JoaogSacerdote/CyberGame/assets/sprites/IMAGENS_ANTIGAS/empresa/AREA_DE_INTERACAO_BAIXO_DO_NPC_TI_NULL.png

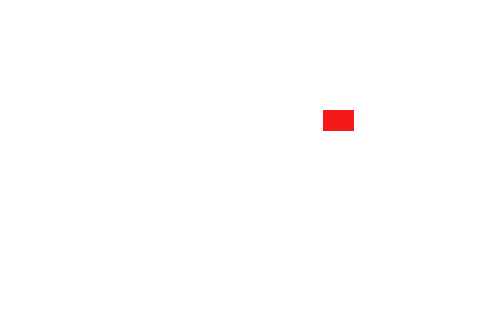
assets/sprites/IMAGENS_ANTIGAS/empresa/AREA_DE_INTERACAO_BAIXO_DO_NPC_TI_NULL.png
