JoaogSacerdote/CyberGame/assets/sprites/IMAGENS_ANTIGAS/empresa/AREA_DE_INTERACAO_PARA_TAREFA_VERDE_NULL.png

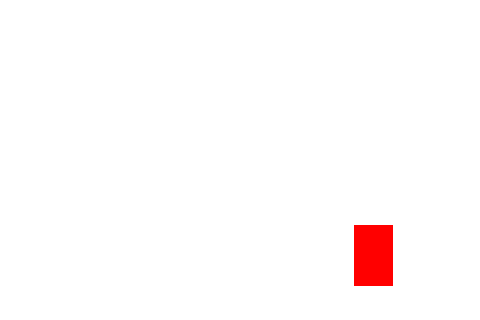
assets/sprites/IMAGENS_ANTIGAS/empresa/AREA_DE_INTERACAO_PARA_TAREFA_VERDE_NULL.png
