JoaogSacerdote/CyberGame/assets/sprites/IMAGENS_ANTIGAS/empresa/AREA_PORTA_RECEPCAO_NULL.png

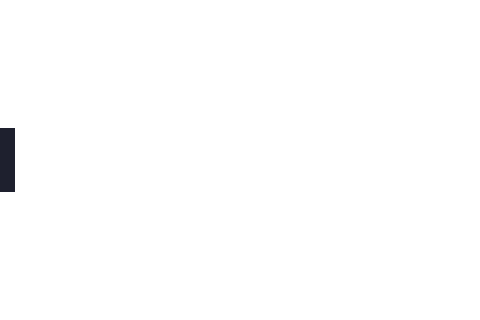
assets/sprites/IMAGENS_ANTIGAS/empresa/AREA_PORTA_RECEPCAO_NULL.png
