JoaogSacerdote/CyberGame/assets/sprites/IMAGENS_ANTIGAS/empresa/CHAO_02.png

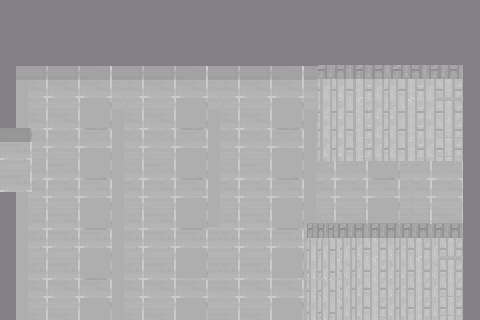
assets/sprites/IMAGENS_ANTIGAS/empresa/CHAO_02.png
