JoaogSacerdote/CyberGame/assets/sprites/IMAGENS_ANTIGAS/empresa/PAREDES.png

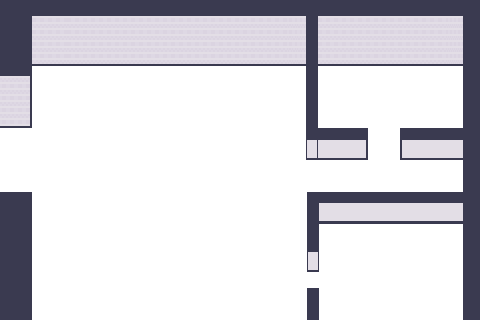
assets/sprites/IMAGENS_ANTIGAS/empresa/PAREDES.png
