JoaogSacerdote/CyberGame/assets/sprites/IMAGENS_ANTIGAS/empresa/PAREDES_E_OBJETOS_02.png

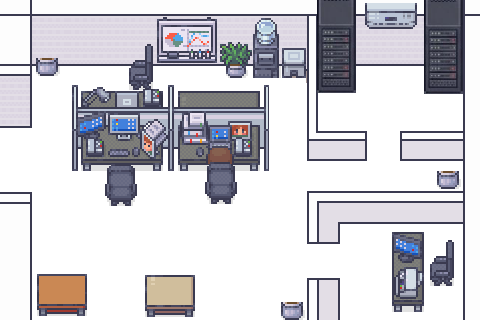
assets/sprites/IMAGENS_ANTIGAS/empresa/PAREDES_E_OBJETOS_02.png
