JoaogSacerdote/CyberGame/assets/sprites/IMAGENS_ANTIGAS/empresa/SPAWN_NULL.png

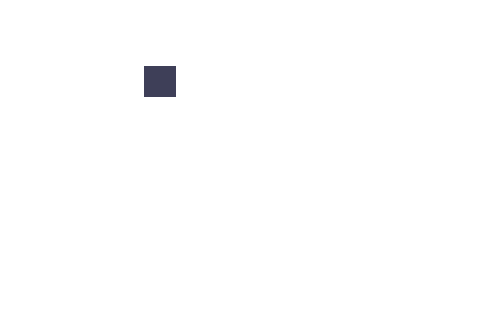
assets/sprites/IMAGENS_ANTIGAS/empresa/SPAWN_NULL.png
