JoaogSacerdote/CyberGame/assets/sprites/IMAGENS_ANTIGAS/recepcao/AREA_QUE_LIBERA_INTERACAO_COM_RECEPCIONISTA_NULL.png

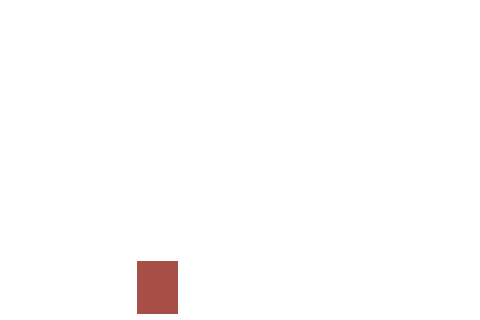
assets/sprites/IMAGENS_ANTIGAS/recepcao/AREA_QUE_LIBERA_INTERACAO_COM_RECEPCIONISTA_NULL.png
