JoaogSacerdote/CyberGame/assets/sprites/IMAGENS_ANTIGAS/recepcao/COMPLEMENTO_SEMCOLISAO_PAREDES_E_OBJETOS_03.png

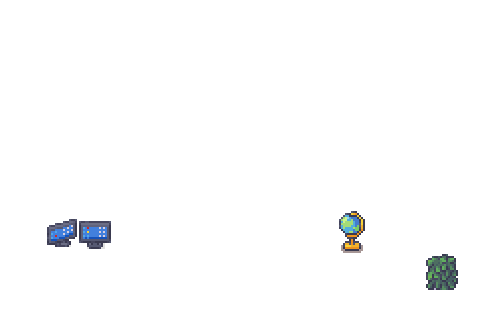
assets/sprites/IMAGENS_ANTIGAS/recepcao/COMPLEMENTO_SEMCOLISAO_PAREDES_E_OBJETOS_03.png
