JoaogSacerdote/CyberGame/assets/sprites/IMAGENS_ANTIGAS/recepcao/PAREDES.png

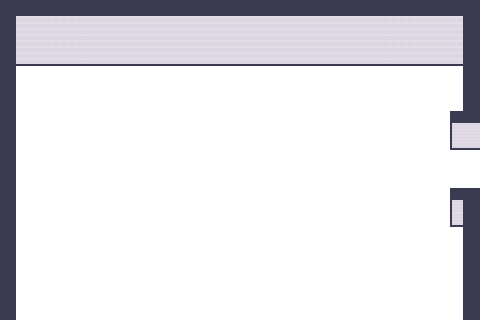
assets/sprites/IMAGENS_ANTIGAS/recepcao/PAREDES.png
