JoaogSacerdote/CyberGame/assets/sprites/IMAGENS_ANTIGAS/recepcao/PISO_CAMADA_00.png

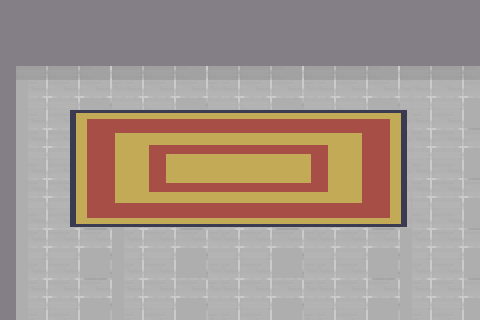
assets/sprites/IMAGENS_ANTIGAS/recepcao/PISO_CAMADA_00.png
