JoaogSacerdote/CyberGame/assets/sprites/IMAGENS_ANTIGAS/recepcao/RECEPCIONISTA_MECHENDO_NO_COMPUTADOR_SEM_INTERACAO_05.png

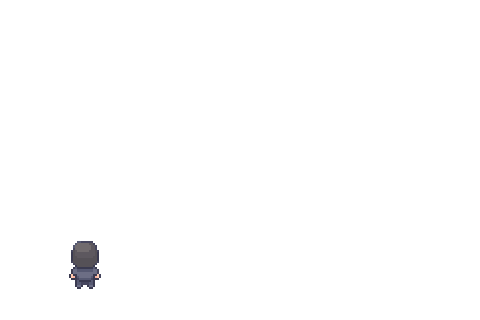
assets/sprites/IMAGENS_ANTIGAS/recepcao/RECEPCIONISTA_MECHENDO_NO_COMPUTADOR_SEM_INTERACAO_05.png
