JoaogSacerdote/CyberGame/assets/sprites/tarefas/CHIADO.png

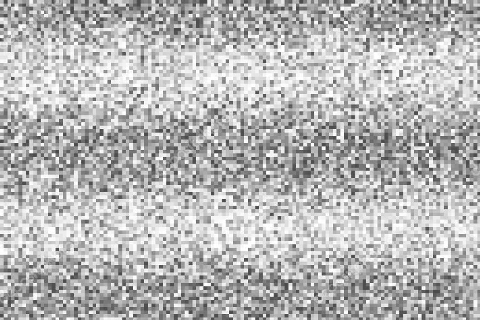
assets/sprites/tarefas/CHIADO.png
