JoaogSacerdote/CyberGame/assets/sprites/tarefas/CREDENCIAL_GERAL.png

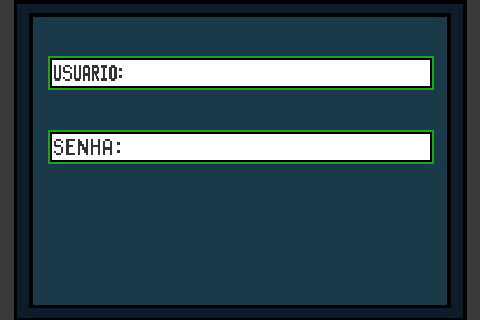
assets/sprites/tarefas/CREDENCIAL_GERAL.png
