JoaogSacerdote/CyberGame/assets/sprites/tarefas/FUNDO_TELA.png

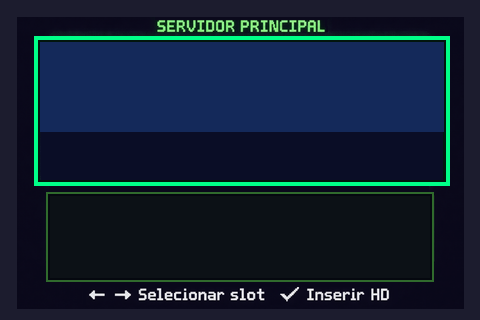
assets/sprites/tarefas/FUNDO_TELA.png
