JoaogSacerdote/CyberGame/assets/sprites/tarefas/SERVIDOR_FUNDO.png

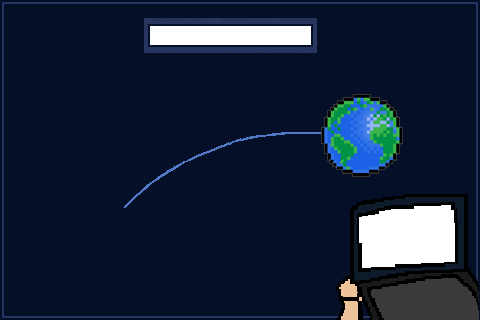
assets/sprites/tarefas/SERVIDOR_FUNDO.png
