JoaogSacerdote/CyberGame/assets/sprites/tarefas/TELA_DERROTA.png

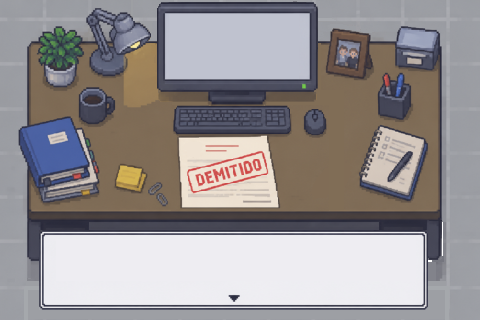
assets/sprites/tarefas/TELA_DERROTA.png
