JoaogSacerdote/CyberGame/assets/sprites/tarefas/TELA_VITORIA.png

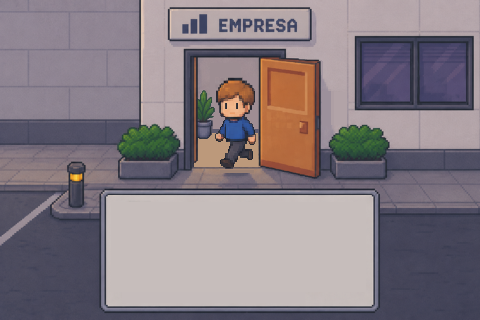
assets/sprites/tarefas/TELA_VITORIA.png
