JoaogSacerdote/CyberGame/simulation/img/Tela01.png

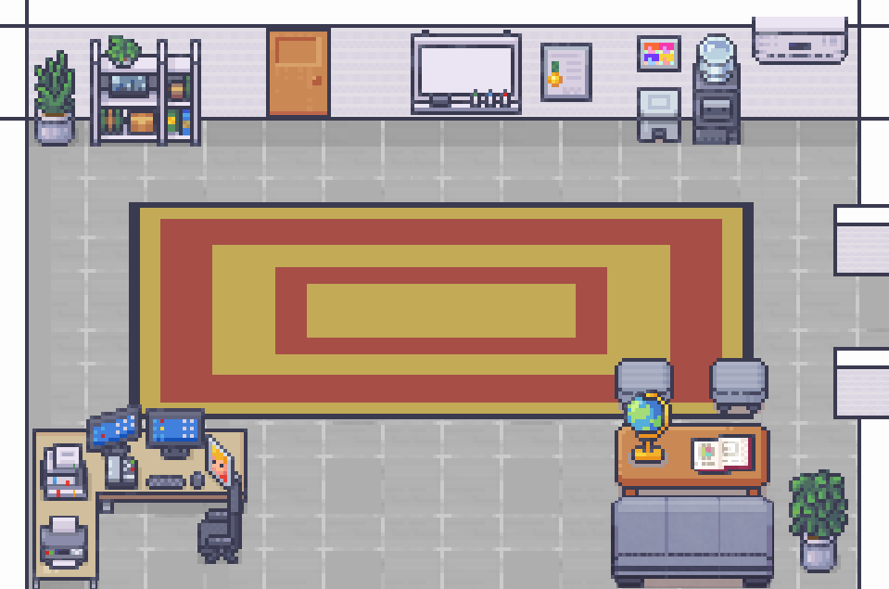
simulation/img/Tela01.png
