JoaogSacerdote/CyberGame/simulation/img/Tela02.png

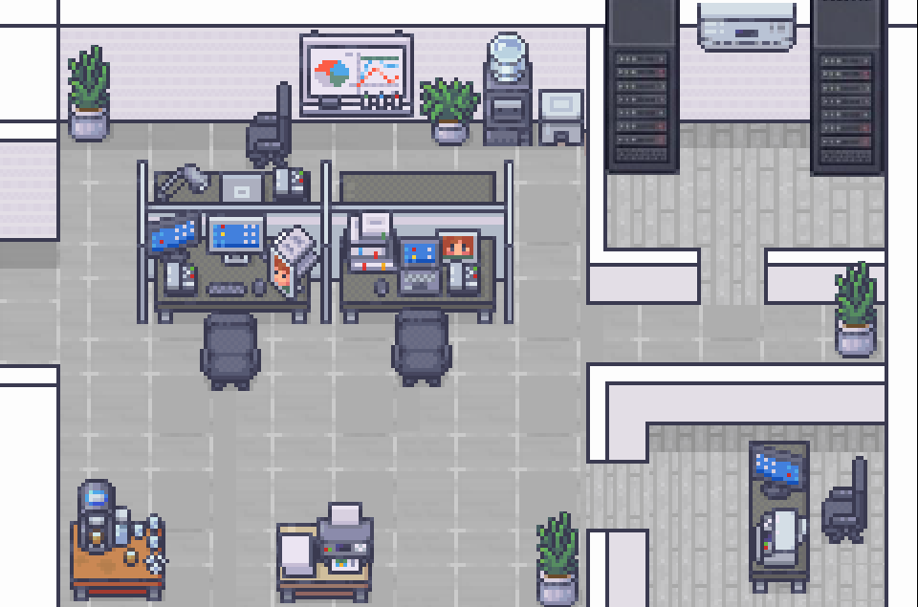
simulation/img/Tela02.png
