JoaogSacerdote/CyberGame/simulation/img/tela_inicial.png

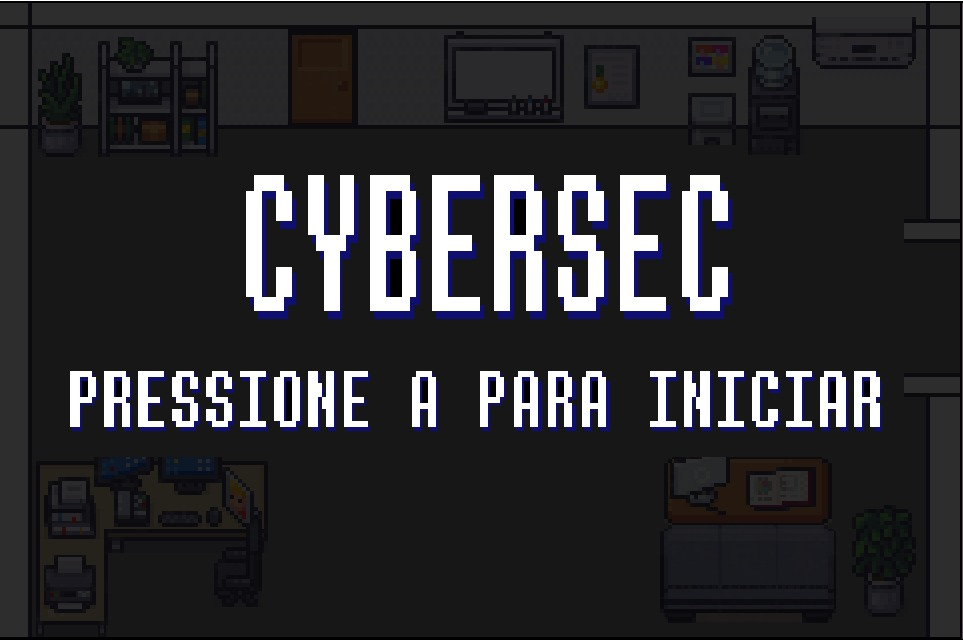
simulation/img/tela_inicial.png
