JoaogSacerdote/CyberGame/hardware/esquematico/CyberGame.kicad_sch

## KiCad design hardware/esquematico/CyberGame.kicad_sch (2026-06-06)

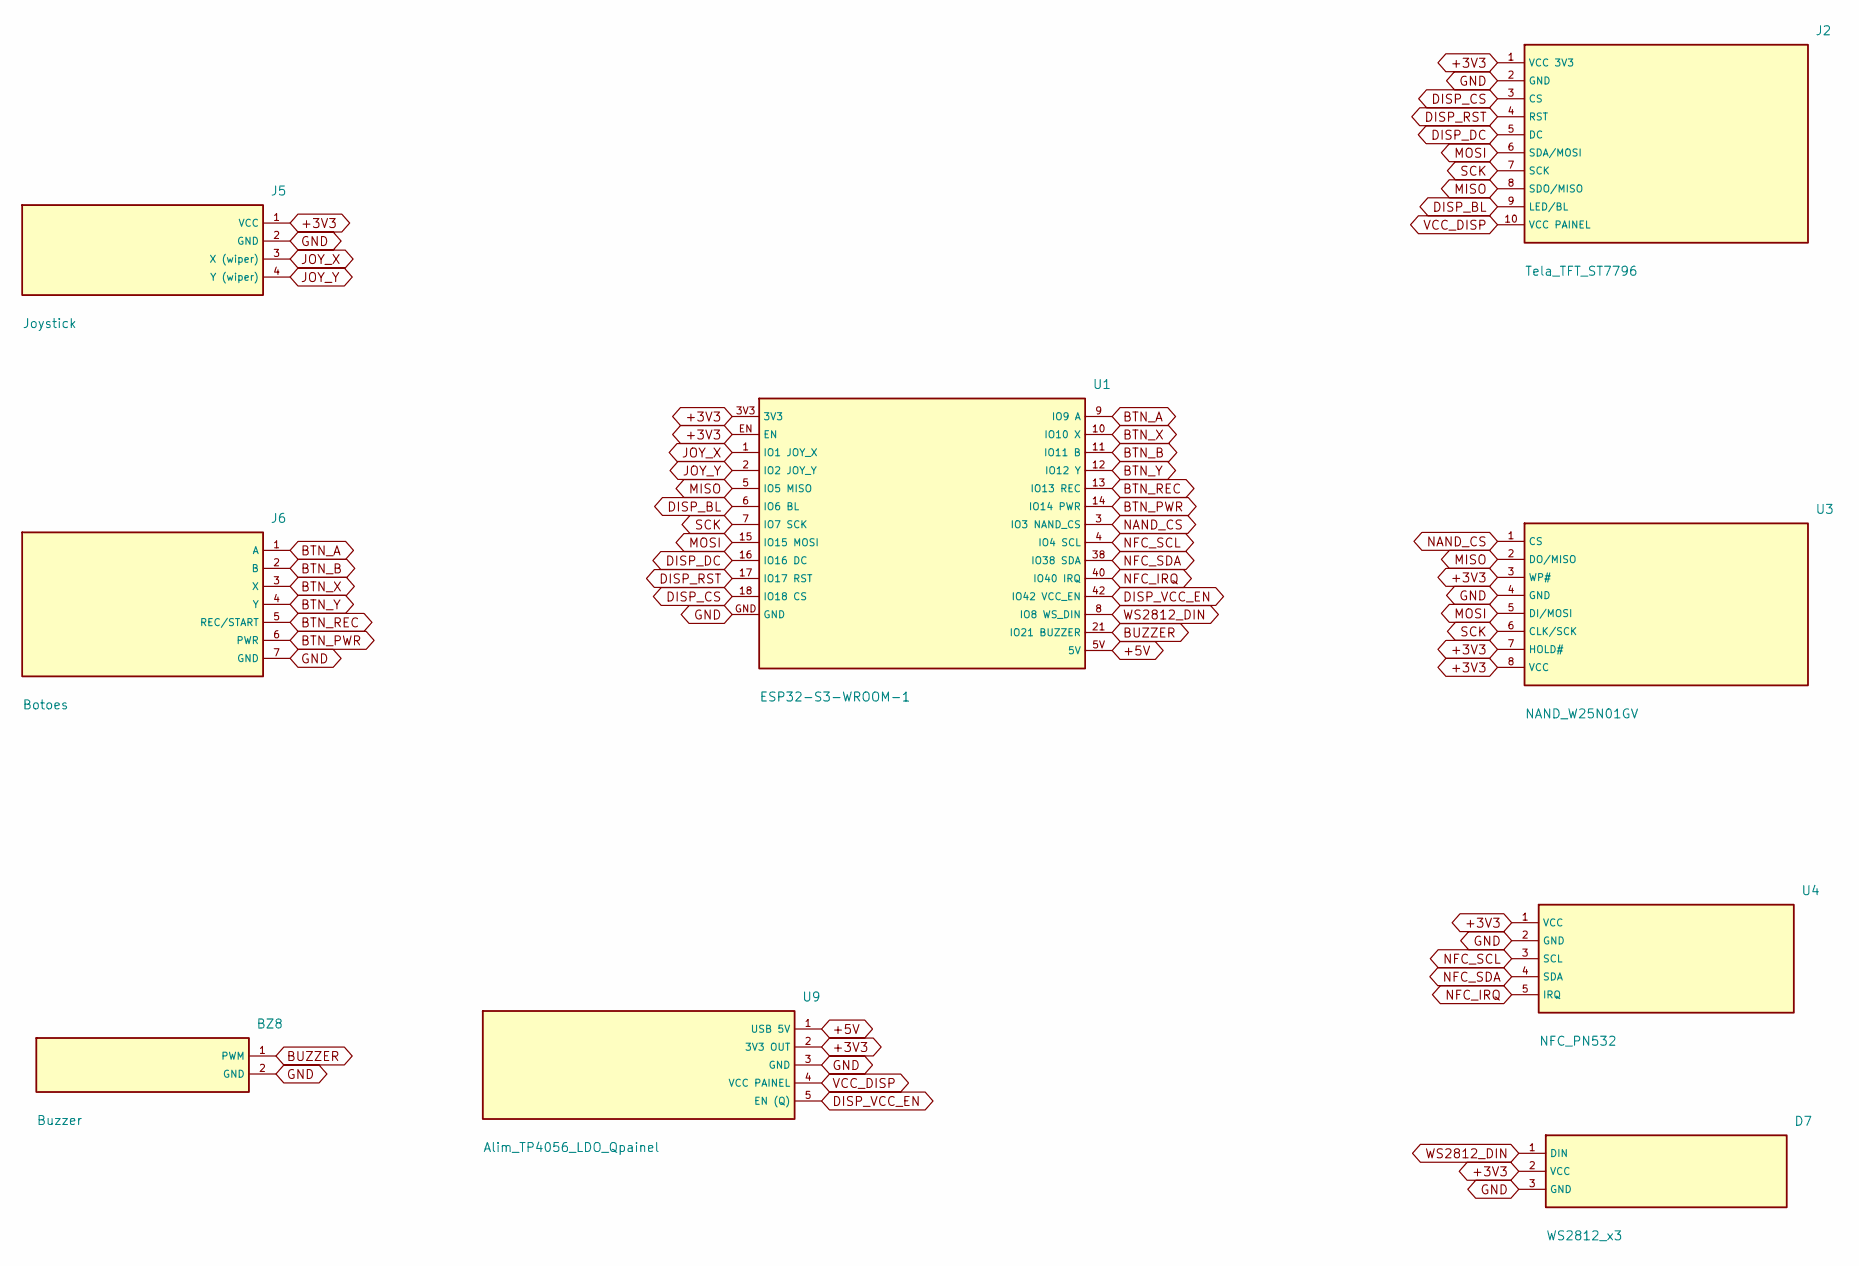
[picture p45: schematic CyberGame.kicad_sch]

Parts:
BZ8: Buzzer
D7: WS2812_x3
J2: Tela_TFT_ST7796
J5: Joystick
J6: Botoes
U1: ESP32-S3-WROOM-1
U3: NAND_W25N01GV
U4: NFC_PN532
U9: Alim_TP4056_LDO_Qpainel

Connections:
+3V3: D7.2 (VCC), J2.1 (VCC 3V3), J5.1 (VCC), U1.3V3, U1.EN, U3.3 (WP#), U3.7 (HOLD#), U3.8 (VCC), U4.1 (VCC), U9.2 (3V3 OUT)
+5V: U1.5V, U9.1 (USB 5V)
BTN_A: J6.1 (A), U1.9 (IO9 A)
BTN_B: J6.2 (B), U1.11 (IO11 B)
BTN_PWR: J6.6 (PWR), U1.14 (IO14 PWR)
BTN_REC: J6.5 (REC/START), U1.13 (IO13 REC)
BTN_X: J6.3 (X), U1.10 (IO10 X)
BTN_Y: J6.4 (Y), U1.12 (IO12 Y)
BUZZER: BZ8.1 (PWM), U1.21 (IO21 BUZZER)
DISP_BL: J2.9 (LED/BL), U1.6 (IO6 BL)
DISP_CS: J2.3 (CS), U1.18 (IO18 CS)
DISP_DC: J2.5 (DC), U1.16 (IO16 DC)
DISP_RST: J2.4 (RST), U1.17 (IO17 RST)
DISP_VCC_EN: U1.42 (IO42 VCC_EN), U9.5 (EN (Q))
GND: BZ8.2 (GND), D7.3 (GND), J2.2 (GND), J5.2 (GND), J6.7 (GND), U1.GND, U3.4 (GND), U4.2 (GND), U9.3 (GND)
JOY_X: J5.3 (X (wiper)), U1.1 (IO1 JOY_X)
JOY_Y: J5.4 (Y (wiper)), U1.2 (IO2 JOY_Y)
MISO: J2.8 (SDO/MISO), U1.5 (IO5 MISO), U3.2 (DO/MISO)
MOSI: J2.6 (SDA/MOSI), U1.15 (IO15 MOSI), U3.5 (DI/MOSI)
NAND_CS: U1.3 (IO3 NAND_CS), U3.1 (CS)
NFC_IRQ: U1.40 (IO40 IRQ), U4.5 (IRQ)
NFC_SCL: U1.4 (IO4 SCL), U4.3 (SCL)
NFC_SDA: U1.38 (IO38 SDA), U4.4 (SDA)
SCK: J2.7 (SCK), U1.7 (IO7 SCK), U3.6 (CLK/SCK)
VCC_DISP: J2.10 (VCC PAINEL), U9.4 (VCC PAINEL)
WS2812_DIN: D7.1 (DIN), U1.8 (IO8 WS_DIN)
