JoaogSacerdote/CyberGame/components/hardware/include/buzzer_melodies.h

#pragma once
/* buzzer_melodies.h — gerado por tools/midi_to_buzzer.py — NAO EDITE */
/* Formato de cada entrada: { freq_hz, duration_ms }                  */
/* freq_hz == 0 significa silencio (pausa).                           */
#include <stdint.h>

/* RECEPCAO — 562 notas */
static const uint16_t melody_recepcao[][2] = {
    {  415,   231},
    {   87,   231},
    {    0,   462},
    {  554,   231},
    {    0,   231},
    {  415,   231},
    {   69,   693},
    {  659,   231},
    {    0,   231},
    {  415,   231},
    {   69,   231},
    {  831,   231},
    {    0,   231},
    {  415,   231},
    {   87,   231},
    {    0,   462},
    {  523,   231},
    {    0,   231},
    {  415,   231},
    {   69,   693},
    {  659,   231},
    {    0,   231},
    {  415,   231},
    {   69,   231},
    {  831,   231},
    {    0,   231},
    {  415,   231},
    {   87,   231},
    {    0,   462},
    {  554,   231},
    {    0,   231},
    {  415,   231},
    {   69,   693},
    {  659,   231},
    {    0,   231},
    {  415,   231},
    {   69,   231},
    {  831,   231},
    {    0,   231},
    {  415,   231},
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
};
#define MELODY_RECEPCAO_LEN  562u

/* ESCRITORIO — 617 notas */
static const uint16_t melody_escritorio[][2] = {
    {  139,   353},
    {  277,   176},
    {    0,   176},
    {  139,   353},
    {  208,   176},
    {    0,   176},
    {  277,   176},
    {  139,   529},
    {  330,   176},
    {  139,   176},
    {  415,   176},
    {  139,   176},
    {  110,   353},
    {  262,   176},
    {    0,   176},
    {  110,   353},
    {  220,   176},
    {    0,   176},
    {  262,   176},
    {  110,   529},
    {  330,   176},
    {  110,   176},
    {  440,   176},
    {  110,   176},
    {  104,   353},
    {  247,   176},
    {    0,   176},
    {  104,   353},
    {  208,   176},
    {    0,   176},
    {  247,   176},
    {  104,   529},
    {  311,   176},
    {  104,   176},
    {  415,   176},
    {  104,   176},
    {   98,   353},
    {  233,   176},
    {    0,   176},
    {  175,   353},
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
};
#define MELODY_ESCRITORIO_LEN  617u

/* ATAQUE — 987 notas */
static const uint16_t melody_ataque[][2] = {
    {   98,   316},
    {  466,   158},
    {    0,   158},
    {   98,   316},
    {  392,   158},
    {    0,   158},
    {  466,   158},
    {   98,   474},
    {  349,   158},
    {   87,   158},
    {  415,   158},
    {   87,   158},
    {   98,   316},
    {  466,   158},
    {    0,   158},
    {   98,   316},
    {  392,   158},
    {    0,   158},
    {  466,   158},
    {   98,   474},
    {  392,   158},
    {   98,   158},
    {  466,   158},
    {   98,   474},
    {  466,   158},
    {    0,   158},
    {   98,   316},
    {  392,   158},
    {    0,   158},
    {  466,   158},
    {   98,   474},
    {  349,   158},
    {   87,   158},
    {  415,   158},
    {   87,   158},
    {   98,   316},
    {  466,   158},
    {    0,   158},
    {   98,   316},
    {  392,   158},
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
};
#define MELODY_ATAQUE_LEN  987u
