JoaogSacerdote/CyberGame/components/hardware/include/pmu.h

#pragma once

#include <stdbool.h>
#include "esp_err.h"

/* Pino do PMU vive em components/hardware/include/board_pins.h
 * (BOARD_PIN_PMU_PWR). Header publico do PMU nao precisa expor o GPIO —
 * eh detalhe de implementacao. */

#define PMU_HOLD_BOOT_MS        2000
#define PMU_HOLD_SHUTDOWN_MS    4000

typedef enum {
    PMU_BOOT_ABORT     = 0,  /* PWR solto antes do hold completar — voltar para Deep Sleep */
    PMU_BOOT_NORMAL,         /* PWR segurado por 2s — fluxo normal do jogo */
} pmu_boot_mode_t;

#ifdef __cplusplus
extern "C" {
#endif

esp_err_t       pmu_init(void);
pmu_boot_mode_t pmu_check_boot_mode(void);
void            pmu_enter_deep_sleep(void);
void            pmu_shutdown_monitor_task(void *pvParameters);

#ifdef __cplusplus
}
#endif
